alesskerbinek/FlightSimPanel/Docu/Resource/command-config.PNG

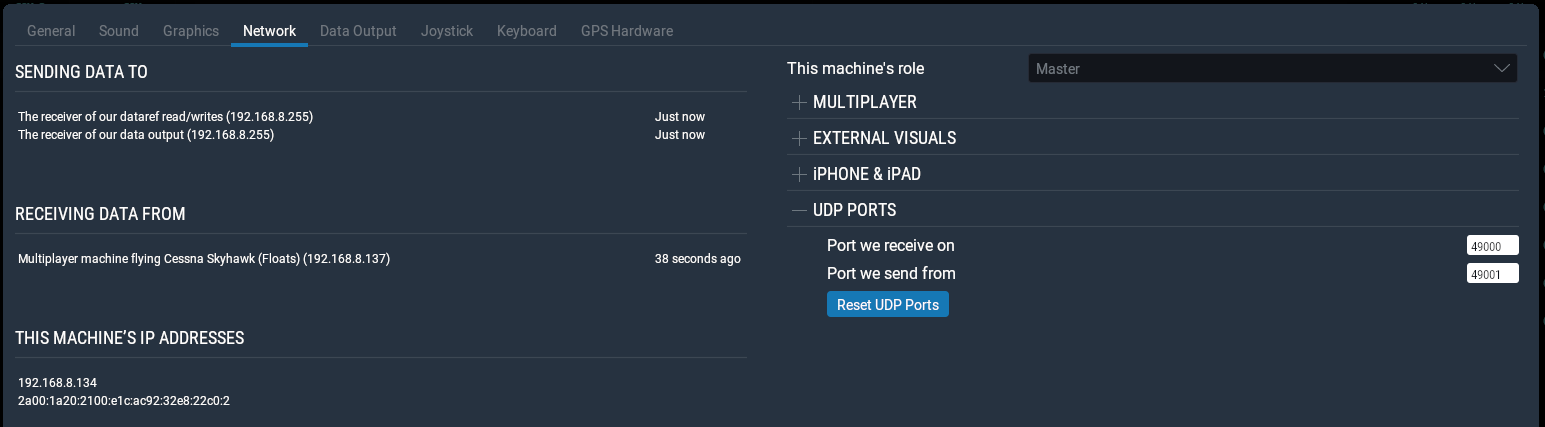
Docu/Resource/command-config.PNG
