alesskerbinek/FlightSimPanel/Docu/Resource/dataref-config.PNG

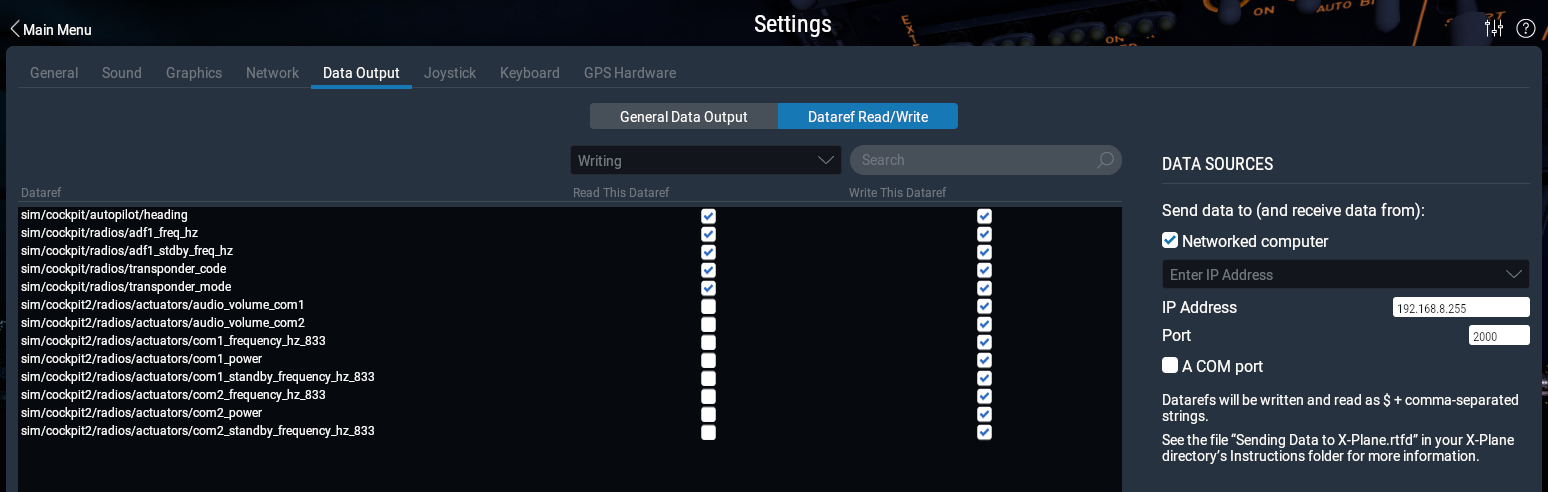
Docu/Resource/dataref-config.PNG
