alesskerbinek/FlightSimPanel/Docu/Resource/Garmin-Radio.png

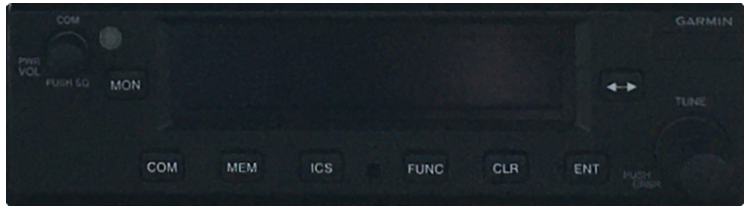
Docu/Resource/Garmin-Radio.png
