alesskerbinek/FlightSimPanel/Docu/Resource/GTX328.png

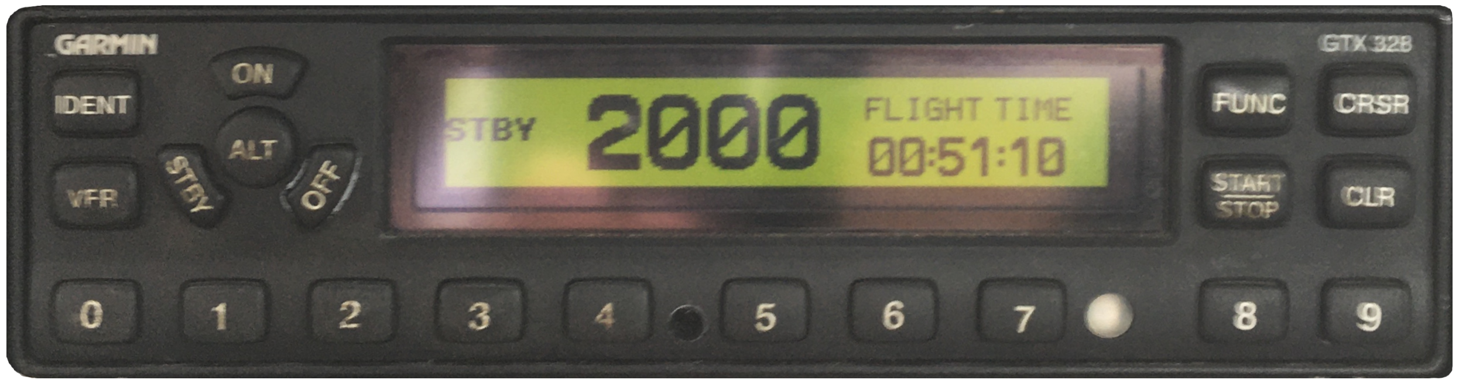
Docu/Resource/GTX328.png
