alesskerbinek/FlightSimPanel/Docu/Resource/KR87.png

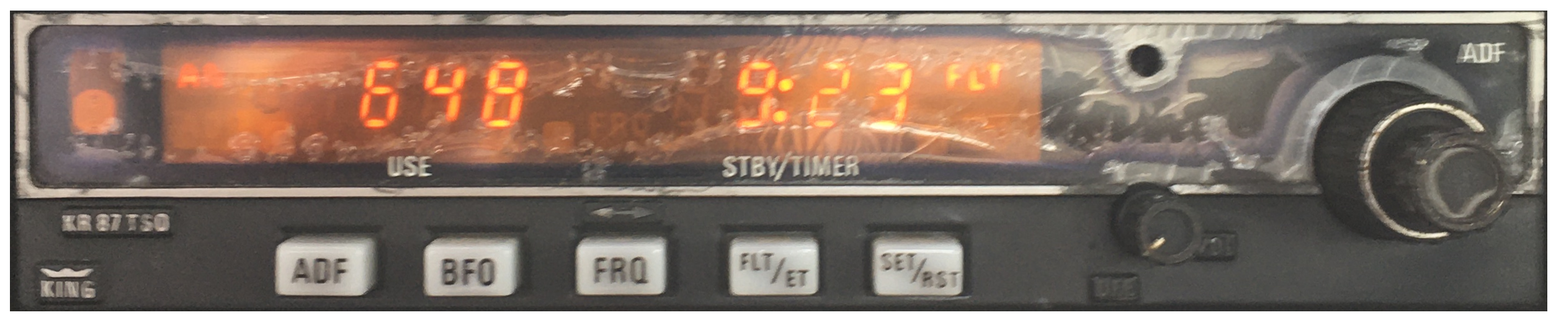
Docu/Resource/KR87.png
