alesskerbinek/FlightSimPanel/Docu/Resource/Trig_TY96.png

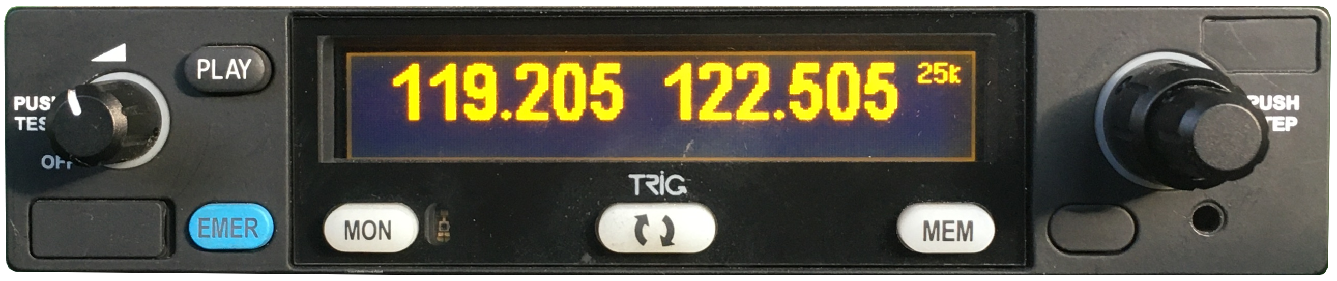
Docu/Resource/Trig_TY96.png
