alesskerbinek/FlightSimPanel/Scratch/IMG_7697.JPG

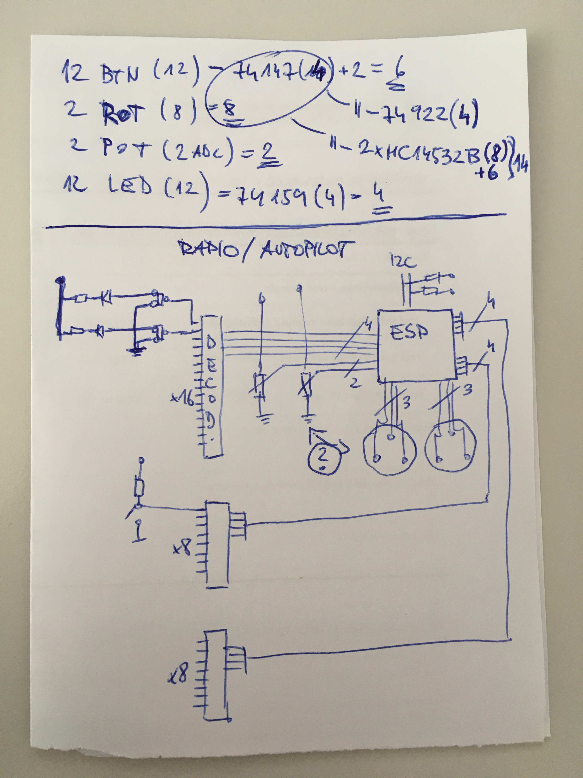
Scratch/IMG_7697.JPG
