alesskerbinek/FlightSimPanel/Scratch/IMG_7699.JPG

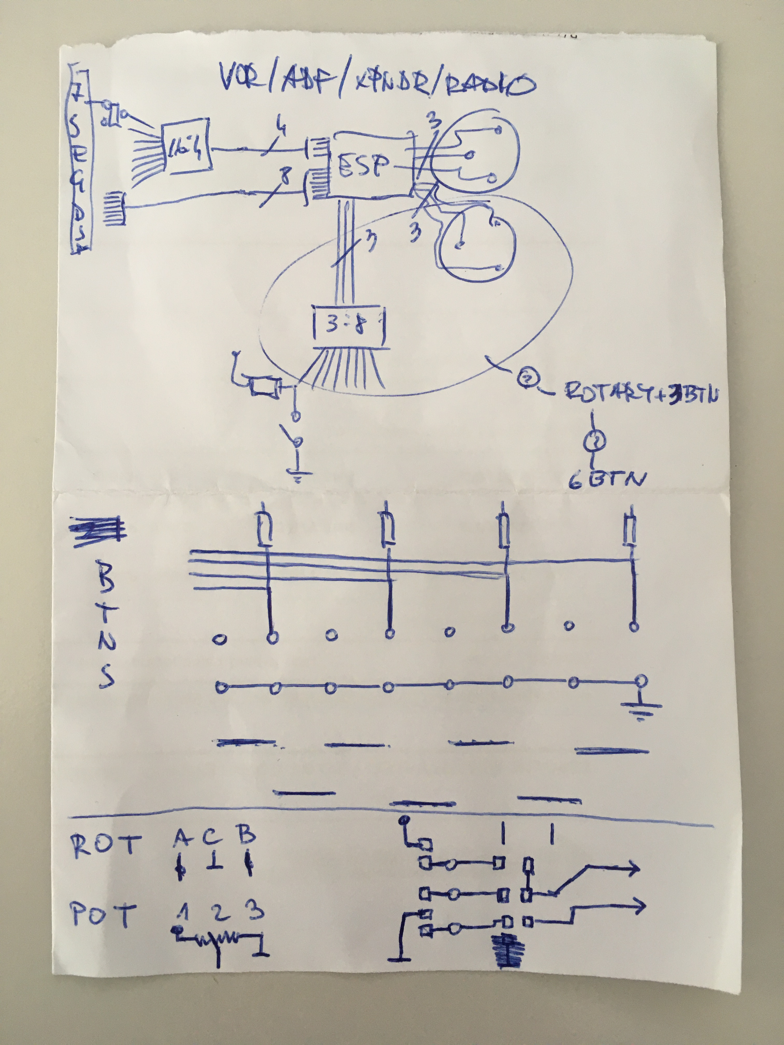
Scratch/IMG_7699.JPG
