alesskerbinek/FlightSimPanel/Scratch/IMG_8052.JPG

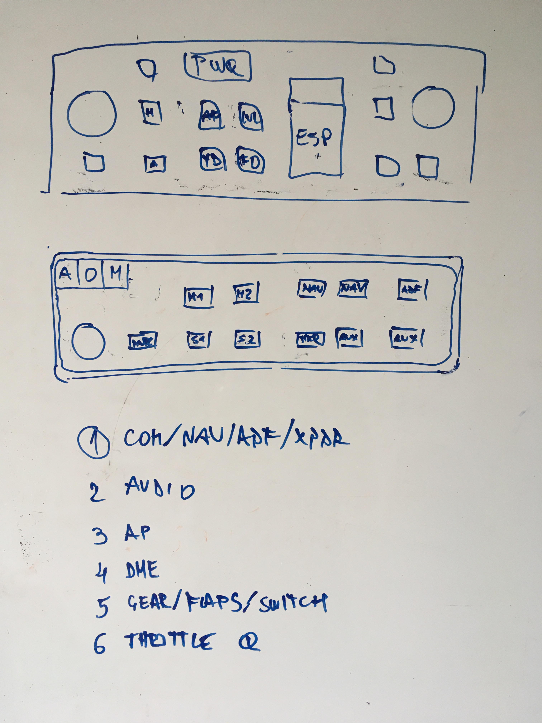
Scratch/IMG_8052.JPG
